Pranav2008-droid/PLL-SSTC/attiny85_song_player/song_data.h

#ifndef SONG_DATA_H
#define SONG_DATA_H

#include <avr/pgmspace.h>

struct CompressedNote {
  uint8_t note_idx;
  uint8_t ticks;
};

const uint16_t note_freqs[] PROGMEM = {
  0, 131, 139, 147, 156, 165, 175, 185, 196, 208, 220, 233, 247, 262, 277, 294, 311, 330, 349, 370, 392, 415, 440, 466, 494, 523, 554, 587, 622, 659, 698, 740, 784, 831, 880, 932, 988
};

const CompressedNote full_midi_song[] PROGMEM = {
  {0,40}, {1,53}, {3,6}, {1,13}, {3,6}, {1,13}, {3,6}, {1,13}, {3,6}, {1,13}, 
  {3,6}, {1,13}, {3,6}, {1,13}, {3,6}, {1,13}, {3,6}, {1,13}, {3,6}, {1,13}, 
  {3,6}, {1,13}, {3,6}, {1,13}, {3,6}, {1,13}, {3,6}, {1,13}, {3,6}, {1,13}, 
  {3,6}, {1,13}, {3,6}, {34,76}, {30,38}, {22,38}, {23,67}, {25,4}, {23,5}, 
  {22,76}, {34,33}, {10,5}, {29,38}, {26,38}, {22,33}, {35,72}, {36,4}, {35,5}, 
  {34,95}, {30,19}, {27,19}, {22,19}, {27,19}, {30,19}, {34,14}, {3,5}, 
  {27,14}, {35,72}, {36,4}, {35,5}, {34,95}, {29,19}, {26,19}, {22,19}, 
  {26,19}, {29,19}, {34,14}, {10,5}, {22,14}, {10,1}, {32,72}, {30,4}, {29,5}, 
  {30,76}, {27,14}, {3,5}, {1,13}, {3,6}, {1,13}, {3,6}, {1,13}, {3,6}, {1,13}, 
  {3,6}, {1,13}, {3,6}, {1,13}, {3,6}, {1,13}, {3,6}, {1,13}, {3,6}, {1,13}, 
  {3,6}, {1,13}, {3,6}, {1,13}, {3,6}, {1,13}, {3,6}, {1,13}, {3,6}, {1,13}, 
  {3,6}, {1,13}, {3,6}, {1,13}, {3,44}, {1,13}, {3,25}, {1,13}, {6,19}, {3,25}, 
  {1,13}, {8,44}, {1,13}, {8,6}, {10,25}, {1,7}, {10,20}, {9,5}, {10,14}, 
  {9,5}, {1,13}, {10,82}, {1,13}, {10,6}, {1,13}, {10,25}, {1,13}, {8,6}, 
  {11,14}, {10,5}, {11,14}, {10,5}, {11,14}, {8,5}, {10,51}, {15,6}, {27,25}, 
  {25,3}, {1,3}, {3,44}, {1,13}, {3,25}, {1,13}, {6,19}, {3,25}, {1,13}, 
  {8,63}, {10,25}, {1,7}, {10,20}, {9,5}, {10,14}, {9,5}, {1,13}, {10,81}, 
  {1,13}, {10,6}, {1,13}, {10,25}, {1,13}, {8,6}, {11,33}, {10,5}, {11,14}, 
  {8,5}, {10,51}, {15,6}, {27,33}, {3,5}, {1,13}, {3,6}, {1,13}, {3,6}, {1,13}, 
  {3,6}, {1,13}, {3,6}, {1,13}, {3,6}, {1,13}, {3,6}, {1,13}, {3,6}, {1,13}, 
  {3,6}, {1,13}, {3,6}, {1,13}, {3,6}, {1,13}, {3,6}, {1,13}, {3,6}, {1,13}, 
  {3,6}, {1,13}, {3,6}, {1,13}, {3,6}, {34,76}, {30,38}, {22,38}, {23,67}, 
  {25,4}, {23,5}, {22,76}, {34,33}, {17,5}, {29,38}, {26,38}, {22,32}, {17,1}, 
  {35,72}, {36,4}, {35,5}, {34,95}, {30,19}, {27,19}, {22,19}, {27,19}, 
  {30,19}, {34,14}, {18,5}, {27,13}, {18,1}, {35,72}, {36,4}, {35,5}, {34,95}, 
  {29,19}, {26,19}, {22,19}, {26,19}, {29,19}, {34,14}, {17,5}, {22,14}, 
  {32,72}, {30,4}, {29,5}, {30,76}, {27,14}, {3,5}, {1,13}, {3,6}, {1,13}, 
  {3,6}, {1,13}, {3,6}, {1,13}, {3,6}, {1,13}, {3,6}, {1,13}, {3,6}, {1,13}, 
  {3,6}, {15,18}, {1,13}, {15,24}, {1,13}, {15,24}, {1,13}, {15,24}, {1,13}, 
  {15,24}, {3,13}, {15,24}, {1,13}, {15,24}, {1,13}, {15,60}, {8,13}, {15,24}, 
  {1,13}, {15,6}, {13,19}, {10,6}, {1,7}, {13,44}, {14,18}, {10,13}, {14,24}, 
  {10,13}, {14,24}, {1,13}, {14,42}, {15,18}, {11,13}, {15,24}, {11,13}, 
  {15,24}, {8,13}, {15,19}, {2,4}, {27,25}, {25,7}, {15,6}, {3,13}, {15,24}, 
  {3,13}, {15,24}, {1,13}, {15,60}, {8,13}, {15,23}, {8,13}, {15,6}, {13,19}, 
  {10,6}, {1,7}, {13,44}, {14,18}, {10,13}, {14,24}, {10,13}, {14,24}, {1,13}, 
  {14,42}, {15,18}, {11,13}, {15,24}, {11,13}, {15,24}, {8,13}, {15,19}, {2,4}, 
  {27,31}, {22,6}, {27,6}, {30,6}, {34,6}, {15,6}, {18,6}, {22,6}, {27,6}, 
  {30,6}, {34,6}, {15,6}, {18,6}, {22,6}, {27,6}, {30,6}, {34,6}, {15,6}, 
  {18,6}, {22,6}, {27,6}, {30,6}, {34,7}, {15,6}, {18,6}, {22,6}, {27,6}, 
  {30,6}, {34,6}, {15,6}, {18,6}, {22,6}, {27,6}, {30,6}, {34,6}, {15,6}, 
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
};

const uint16_t full_midi_song_len = 1027;
const uint16_t BASE_TICK_MS = 25;

#endif
